EleDes/3458A_A9_REF_PCB_KICAD/Pictures/3458A Ref A9 Clone 3D top models + cap.png

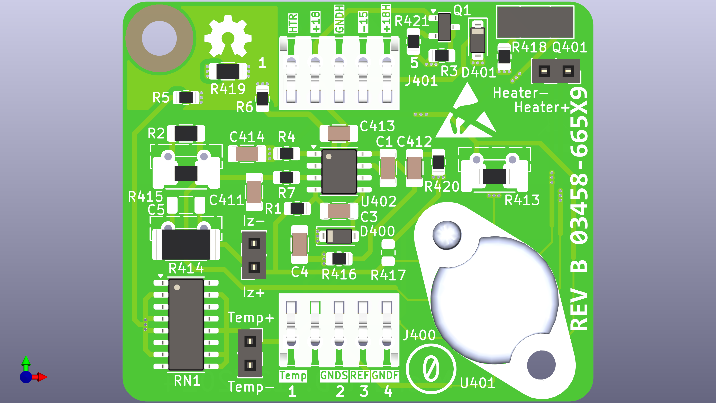
Pictures/3458A Ref A9 Clone 3D top models + cap.png
