EleDes/3458A_A9_REF_PCB_KICAD/Simulations/ADR1000 9.3mA.asc

C1: cap; 100n
C2: cap; 10p
C3: cap; 0.1µ
C4: cap; 10n
D1: diode; 1N4148
D2: diode; 1N4148
Q3: npn; 2N3904
R1: res; {R1}
R2: res; {R2}
R3: res; {R3}
R4: res; {R4}
R5: res; 666.7
R9: res; 1Meg
R11: res; 1k
U2: LT1013
U3: LT1013
U4: ADR1000
V1: voltage; 30
Named nets: 0, REF, TEMP, HEATER+, IZSET, DIODE, DIV, IN
.param R1=50 R2=5k7 R3=62k R4=8k
.tran 0 1000 1m startup
.meas out param V(REF) ; final value of V(REF)
.options numdgt=15 measdgt=10 plotwinsize=0
;.temp -30 -20 -10 0 10 20 30 40
;.step param R1 list 22 33 50 75 120
;.step param R2 list 5k6943 5k7 5k7057 61k938 62k 62k062
;.step param R1 list 50 50.05 120 120.12
;.step param R3 list 62k 62k062
.step param R4 list 8k 8k008
.step param R2 list 5k7 62k
Unheated TC: -31.7ppm/K linear -30 .. 40°C with R2=61k9
zTC with R2=5k7
A lengthy .tran often gives more accurate DC information than a .op.
To see drift vs temp, type Ctrl-L, right click=>Plot .step'ed .meas data
10nF slight overshoot at high ambient temperatures
w/o critically damped
